ronj/teensy-dash/source/PeripheralLayer/Bitmaps.cpp

#include "Bitmaps.h"

#ifdef __AVR__
#include <avr/io.h>
#include <avr/pgmspace.h>
#else
#define PROGMEM
#endif

namespace PeripheralLayer
{
	namespace Bitmaps
	{
		namespace internal
		{
			// 
			//  Image data for tirepressure
			// 

			const uint8_t TirePressureData[] =
			{
				0x00, 0x00, 0xE0, 0x00, 0x00, //                 ###                
				0x00, 0x01, 0xF0, 0x00, 0x00, //                #####               
				0x00, 0x01, 0xF0, 0x00, 0x00, //                #####               
				0x00, 0x01, 0xF0, 0x00, 0x00, //                #####               
				0x00, 0x01, 0xF0, 0x00, 0x00, //                #####               
				0x00, 0x01, 0xF0, 0x00, 0x00, //                #####               
				0x07, 0x01, 0xF0, 0x1C, 0x00, //      ###       #####       ###     
				0x0F, 0x81, 0xF0, 0x3E, 0x00, //     #####      #####      #####    
				0x0F, 0x81, 0xF0, 0x3E, 0x00, //     #####      #####      #####    
				0x0F, 0x81, 0xF0, 0x3E, 0x00, //     #####      #####      #####    
				0x1F, 0x81, 0xF0, 0x3F, 0x00, //    ######      #####      ######   
				0x1F, 0x01, 0xF0, 0x1F, 0x00, //    #####       #####       #####   
				0x3F, 0x01, 0xF0, 0x1F, 0x80, //   ######       #####       ######  
				0x3E, 0x01, 0xF0, 0x0F, 0x80, //   #####        #####        #####  
				0x7E, 0x01, 0xF0, 0x0F, 0xC0, //  ######        #####        ###### 
				0x7C, 0x01, 0xF0, 0x07, 0xC0, //  #####         #####         ##### 
				0x7C, 0x01, 0xF0, 0x07, 0xC0, //  #####         #####         ##### 
				0xF8, 0x01, 0xF0, 0x03, 0xE0, // #####          #####          #####
				0xF8, 0x01, 0xF0, 0x03, 0xE0, // #####          #####          #####
				0xF8, 0x01, 0xF0, 0x03, 0xE0, // #####          #####          #####
				0xF8, 0x00, 0xE0, 0x03, 0xE0, // #####           ###           #####
				0xF8, 0x00, 0x00, 0x03, 0xE0, // #####                         #####
				0xF8, 0x00, 0x40, 0x03, 0xE0, // #####            #            #####
				0xFC, 0x00, 0xE0, 0x07, 0xE0, // ######          ###          ######
				0x7C, 0x01, 0xF0, 0x07, 0xC0, //  #####         #####         ##### 
				0x7C, 0x01, 0xF0, 0x07, 0xC0, //  #####         #####         ##### 
				0x7E, 0x00, 0xE0, 0x0F, 0xC0, //  ######         ###         ###### 
				0x3F, 0x00, 0x00, 0x1F, 0x80, //   ######                   ######  
				0x3F, 0x00, 0x00, 0x1F, 0x80, //   ######                   ######  
				0x1F, 0xFF, 0xFF, 0xFF, 0x00, //    #############################   
				0x0F, 0xFF, 0xFF, 0xFE, 0x00, //     ###########################    
				0x07, 0xFF, 0xFF, 0xFC, 0x00, //      #########################     
				0x07, 0xFF, 0xFF, 0xFC, 0x00, //      #########################     
				0x07, 0xBC, 0xF7, 0xBC, 0x00, //      #### ####  #### #### ####     
				0x07, 0xBC, 0xF7, 0xB8, 0x00, //      #### ####  #### #### ###      
			};

			const uint8_t WaterTemperatureData[] PROGMEM =
			{
				0x00, 0x00, 0x40, 0x00, 0x00, //                  #                 
				0x00, 0x00, 0xE0, 0x00, 0x00, //                 ###                
				0x00, 0x00, 0xE0, 0x00, 0x00, //                 ###                
				0x00, 0x00, 0xE0, 0x00, 0x00, //                 ###                
				0x00, 0x00, 0xE0, 0x00, 0x00, //                 ###                
				0x00, 0x00, 0xFF, 0xE0, 0x00, //                 ###########        
				0x00, 0x00, 0xFF, 0xE0, 0x00, //                 ###########        
				0x00, 0x00, 0xE0, 0x00, 0x00, //                 ###                
				0x00, 0x00, 0xE0, 0x00, 0x00, //                 ###                
				0x00, 0x00, 0xE0, 0x00, 0x00, //                 ###                
				0x00, 0x00, 0xFF, 0xE0, 0x00, //                 ###########        
				0x00, 0x00, 0xFF, 0xE0, 0x00, //                 ###########        
				0x00, 0x00, 0xE0, 0x00, 0x00, //                 ###                
				0x00, 0x00, 0xE0, 0x00, 0x00, //                 ###                
				0x00, 0x00, 0xE0, 0x00, 0x00, //                 ###                
				0x00, 0x00, 0xFF, 0xE0, 0x00, //                 ###########        
				0x00, 0x00, 0xFF, 0xE0, 0x00, //                 ###########        
				0x00, 0x00, 0xE0, 0x00, 0x00, //                 ###                
				0x00, 0x00, 0xE0, 0x00, 0x00, //                 ###                
				0x00, 0x00, 0xE0, 0x00, 0x00, //                 ###                
				0x00, 0x00, 0xE0, 0x00, 0x00, //                 ###                
				0x00, 0x01, 0xF0, 0x00, 0x00, //                #####               
				0xFF, 0x03, 0xF8, 0x1F, 0xE0, // ########      #######      ########
				0xFF, 0xE3, 0xF8, 0xFF, 0xE0, // ###########   #######   ###########
				0xC3, 0xE3, 0xF8, 0xF8, 0x60, // ##    #####   #######   #####    ##
				0x00, 0x01, 0xF0, 0x00, 0x00, //                #####               
				0x00, 0x00, 0xE0, 0x00, 0x00, //                 ###                
				0x00, 0x00, 0x00, 0x00, 0x00, //                                    
				0x00, 0x00, 0x00, 0x00, 0x00, //                                    
				0x3E, 0x3F, 0x1F, 0x8F, 0x80, //   #####   ######   ######   #####  
				0x3F, 0xFF, 0xFF, 0xFF, 0x80, //   ###############################  
				0x03, 0xE1, 0xF0, 0xF8, 0x00, //       #####    #####    #####      
			};

			const uint8_t TripDistanceData[] PROGMEM =
			{
				0x07, 0xF1, 0xFC, 0x00, //      #######   #######     
				0x07, 0xF1, 0xFC, 0x00, //      #######   #######     
				0x07, 0xF1, 0xFC, 0x00, //      #######   #######     
				0x07, 0xF1, 0xFC, 0x00, //      #######   #######     
				0x0F, 0xF1, 0xFE, 0x00, //     ########   ########    
				0x0F, 0xF1, 0xFE, 0x00, //     ########   ########    
				0x0F, 0xF1, 0xFE, 0x00, //     ########   ########    
				0x0F, 0xFF, 0xFE, 0x00, //     ###################    
				0x0F, 0xFF, 0xFE, 0x00, //     ###################    
				0x0F, 0xFF, 0xFE, 0x00, //     ###################    
				0x1F, 0xF1, 0xFF, 0x00, //    #########   #########   
				0x1F, 0xF1, 0xFF, 0x00, //    #########   #########   
				0x1F, 0xF1, 0xFF, 0x00, //    #########   #########   
				0x1F, 0xF1, 0xFF, 0x00, //    #########   #########   
				0x3F, 0xF1, 0xFF, 0x80, //   ##########   ##########  
				0x3F, 0xF1, 0xFF, 0x80, //   ##########   ##########  
				0x3F, 0xF1, 0xFF, 0x80, //   ##########   ##########  
				0x3F, 0xFF, 0xFF, 0x80, //   #######################  
				0x3F, 0xFF, 0xFF, 0x80, //   #######################  
				0x7F, 0xFF, 0xFF, 0xC0, //  ######################### 
				0x7F, 0xF1, 0xFF, 0xC0, //  ###########   ########### 
				0x7F, 0xF1, 0xFF, 0xC0, //  ###########   ########### 
				0x7F, 0xF1, 0xFF, 0xC0, //  ###########   ########### 
				0x7F, 0xF1, 0xFF, 0xC0, //  ###########   ########### 
				0xFF, 0xF1, 0xFF, 0xE0, // ############   ############
				0xFF, 0xF1, 0xFF, 0xE0, // ############   ############
			};

			const uint8_t BatteryData[] PROGMEM =
			{
				0x03, 0xE0, 0x00, 0xF8, 0x00, //       #####             #####      
				0x03, 0xE0, 0x00, 0xF8, 0x00, //       #####             #####      
				0x03, 0xE0, 0x00, 0xF8, 0x00, //       #####             #####      
				0xFF, 0xFF, 0xFF, 0xFF, 0xE0, // ###################################
				0xFF, 0xFF, 0xFF, 0xFF, 0xE0, // ###################################
				0xFF, 0xFF, 0xFF, 0xFF, 0xE0, // ###################################
				0xE0, 0x00, 0x00, 0x00, 0xE0, // ###                             ###
				0xE0, 0x00, 0x00, 0x00, 0xE0, // ###                             ###
				0xE0, 0x00, 0x00, 0x30, 0xE0, // ###                       ##    ###
				0xE0, 0x00, 0x00, 0x30, 0xE0, // ###                       ##    ###
				0xE7, 0xE0, 0x00, 0xFC, 0xE0, // ###  ######             ######  ###
				0xE7, 0xE0, 0x00, 0xFC, 0xE0, // ###  ######             ######  ###
				0xE0, 0x00, 0x00, 0x30, 0xE0, // ###                       ##    ###
				0xE0, 0x00, 0x00, 0x30, 0xE0, // ###                       ##    ###
				0xE0, 0x00, 0x00, 0x00, 0xE0, // ###                             ###
				0xE0, 0x00, 0x00, 0x00, 0xE0, // ###                             ###
				0xE0, 0x00, 0x00, 0x00, 0xE0, // ###                             ###
				0xE0, 0x00, 0x00, 0x00, 0xE0, // ###                             ###
				0xE0, 0x00, 0x00, 0x00, 0xE0, // ###                             ###
				0xE0, 0x00, 0x00, 0x00, 0xE0, // ###                             ###
				0xFF, 0xFF, 0xFF, 0xFF, 0xE0, // ###################################
				0xFF, 0xFF, 0xFF, 0xFF, 0xE0, // ###################################
				0xFF, 0xFF, 0xFF, 0xFF, 0xE0, // ###################################
			};

			const uint8_t FuelPumpData[] PROGMEM =
			{
				0x3F, 0xFE, 0x00, 0x00, //   #############           
				0x7F, 0xFF, 0x00, 0x00, //  ###############          
				0x7F, 0xFF, 0x18, 0x00, //  ###############   ##     
				0x60, 0x03, 0x0C, 0x00, //  ##           ##    ##    
				0x60, 0x03, 0x06, 0x00, //  ##           ##     ##   
				0x60, 0x03, 0x06, 0x00, //  ##           ##     ##   
				0x60, 0x03, 0x07, 0x00, //  ##           ##     ###  
				0x60, 0x03, 0x03, 0x00, //  ##           ##      ##  
				0x60, 0x03, 0x02, 0x00, //  ##           ##      #   
				0x60, 0x03, 0xC2, 0x00, //  ##           ####    #   
				0x7F, 0xFF, 0x62, 0x00, //  ############### ##   #   
				0x7F, 0xFF, 0x23, 0x00, //  ###############  #   ##  
				0x7F, 0xFF, 0x21, 0x00, //  ###############  #    #  
				0x7F, 0xFF, 0x21, 0x00, //  ###############  #    #  
				0x7F, 0xFF, 0x21, 0x80, //  ###############  #    ## 
				0x7F, 0xFF, 0x20, 0x80, //  ###############  #     # 
				0x7F, 0xFF, 0x20, 0x80, //  ###############  #     # 
				0x7F, 0xFF, 0x20, 0xC0, //  ###############  #     ##
				0x7F, 0xFF, 0x20, 0x40, //  ###############  #      #
				0x7F, 0xFF, 0x20, 0x40, //  ###############  #      #
				0x7F, 0xFF, 0x20, 0x40, //  ###############  #      #
				0x7F, 0xFF, 0x20, 0x40, //  ###############  #      #
				0x7F, 0xFF, 0x10, 0x40, //  ###############   #     #
				0x7F, 0xFF, 0x1F, 0x80, //  ###############   ###### 
				0x7F, 0xFF, 0x07, 0x00, //  ###############     ###  
				0xFF, 0xFF, 0x80, 0x00, // #################         
			};

			const uint8_t TimespanData[] PROGMEM =
			{
				0x00, 0x00, 0x70, 0x00, //                  ###          
				0x00, 0x00, 0x7C, 0x00, //                  #####        
				0x00, 0x00, 0x7F, 0x00, //                  #######      
				0x00, 0x00, 0x07, 0x80, //                      ####     
				0x00, 0x00, 0x01, 0xE0, //                        ####   
				0x00, 0x00, 0x00, 0xE0, //                         ###   
				0x00, 0x01, 0xC2, 0x70, //                ###    #  ###  
				0x00, 0x01, 0xC6, 0x38, //                ###   ##   ### 
				0x00, 0x01, 0xC4, 0x18, //                ###   #     ## 
				0x00, 0x01, 0xC0, 0x1C, //                ###         ###
				0x00, 0x01, 0xC0, 0x1C, //                ###         ###
				0x18, 0x01, 0xC0, 0x0C, //    ##          ###          ##
				0x3C, 0x01, 0xC0, 0x0C, //   ####         ###          ##
				0x7E, 0x01, 0xC0, 0xEC, //  ######        ###      ### ##
				0xFF, 0x01, 0xC0, 0xCC, // ########       ###      ##  ##
				0xFF, 0x83, 0x80, 0x0C, // #########     ###           ##
				0x5D, 0x07, 0x80, 0x0C, //  # ### #     ####           ##
				0x0C, 0x0F, 0x00, 0x1C, //     ##      ####           ###
				0x0C, 0x0E, 0x04, 0x18, //     ##      ###      #     ## 
				0x0E, 0x0C, 0x06, 0x38, //     ###     ##       ##   ### 
				0x07, 0x00, 0x02, 0x30, //      ###              #   ##  
				0x07, 0x01, 0x80, 0x70, //      ###       ##        ###  
				0x03, 0xC1, 0x80, 0xE0, //       ####     ##       ###   
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
				0x00, 0x00, 0x00, 0x00, 0x00, 0x00, 0x00, 0x00, 0x00, 0x00, 0x00, 0x00, 0x00, 0x00, 0x00, 0x00,
				0x00, 0x00, 0x00, 0x00, 0x00, 0x00, 0x00, 0x00, 0x00, 0x00, 0x00, 0x00, 0x00, 0x00, 0x00, 0x00
			};
		}
	}
}
