ronj/teensy-dash/source/ApplicationLayer/Models/RepresentableModel.h

#pragma once

#include "Model.h"

namespace ApplicationLayer
{
	namespace Models
	{
		class RepresentableModel : public Model
		{
		public:
			virtual const char* GetFormattedValue() const = 0;
		};
	}
}
