ronj/teensy-dash/source/ApplicationLayer/Models/ConversionHelper.h

#pragma once

#include <cstdio>
#include <cstdarg>

#if defined(_MSC_VER) && _MSC_VER < 1900

#define snprintf c99_snprintf
#define vsnprintf c99_vsnprintf

inline int c99_vsnprintf(char* out, size_t size, const char* format, va_list ap)
{
	int count = -1;

	if (size != 0)
		count = _vsnprintf_s(out, size, _TRUNCATE, format, ap);
	if (count == -1)
		count = _vscprintf(format, ap);

	return count;
}

inline int c99_snprintf(char* out, size_t size, const char* format, ...)
{
	int count;
	va_list ap;

	va_start(ap, format);
	count = c99_vsnprintf(out, size, format, ap);
	va_end(ap);

	return count;
}

#endif
