ronj/teensy-dash/source/HardwareLayer/Teensy/TeensyTimer.cpp

#include "TeensyTimer.h"

#include "Common/ArduinoWrapper.h"

uint32_t HardwareLayer::TeensyTimer::TickCountMilliseconds() const
{
	return millis();
}

uint32_t HardwareLayer::TeensyTimer::TickCountMicroseconds() const
{
	return micros();
}

void HardwareLayer::TeensyTimer::Sleep(uint32_t milliseconds) const
{
	delay(milliseconds);
}
